NQTer/WaterSensorShield/PCB-Board/IMG_2639.JPG

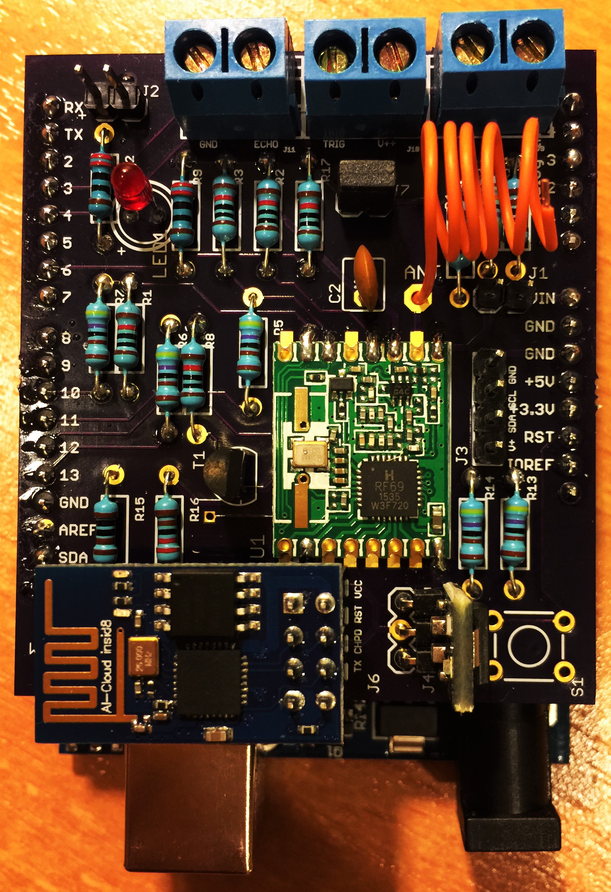
PCB-Board/IMG_2639.JPG
